stefacep/PLUMA-Hotend-Shroud/Photos/1.JPG

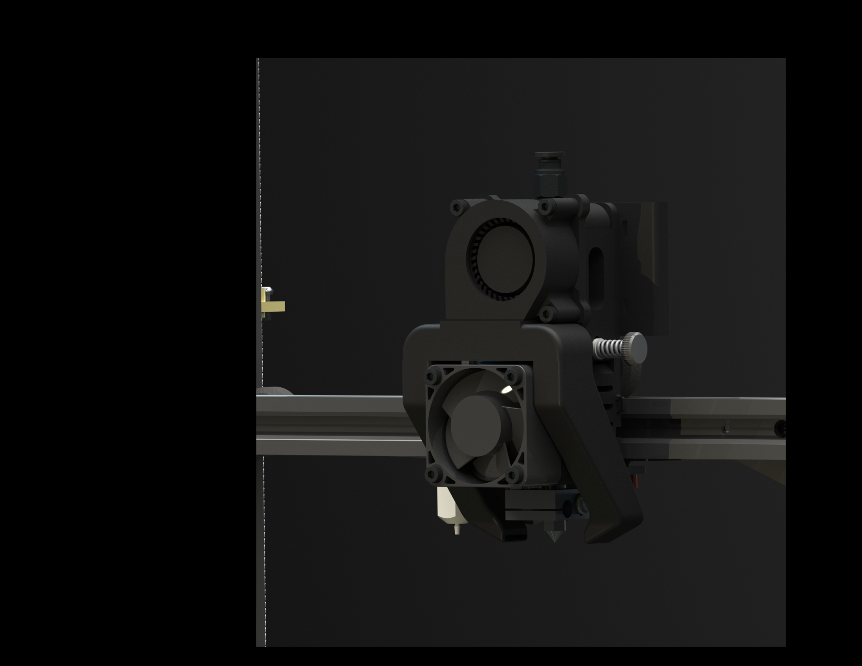
Photos/1.JPG
