stefacep/PLUMA-Hotend-Shroud/Photos/2.jpg

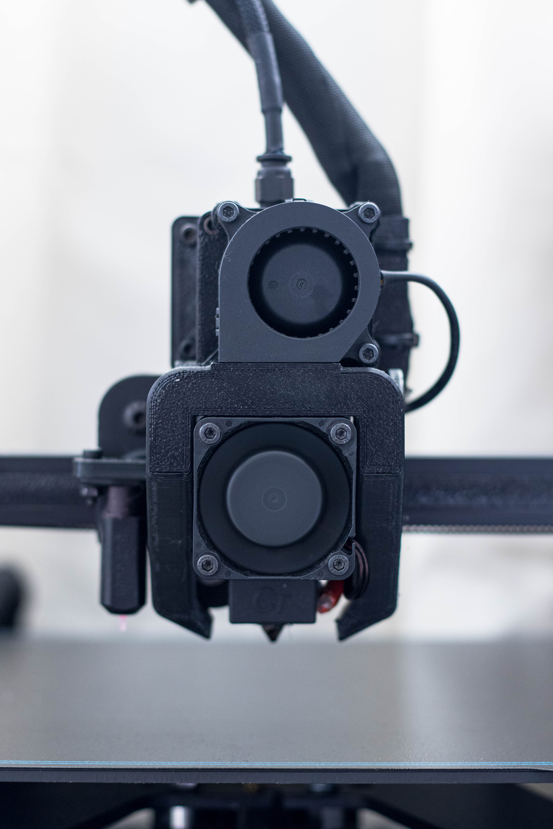
Photos/2.jpg
