stefacep/PLUMA-Hotend-Shroud/Photos/3.jpg

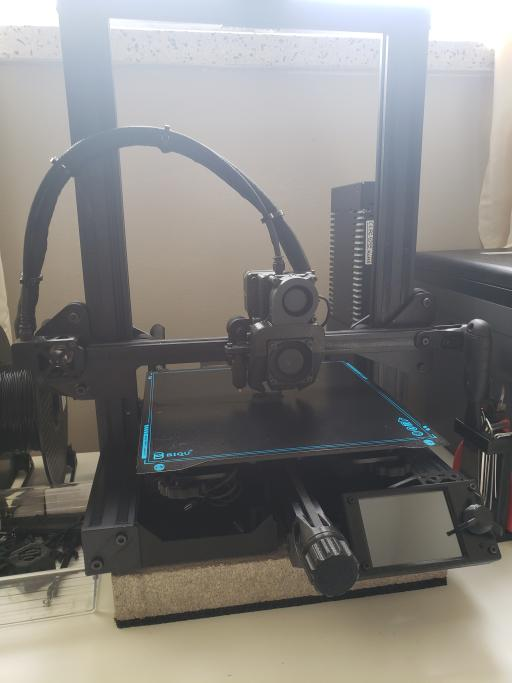
Photos/3.jpg
