stefacep/PLUMA-Hotend-Shroud/Photos/4.jpg

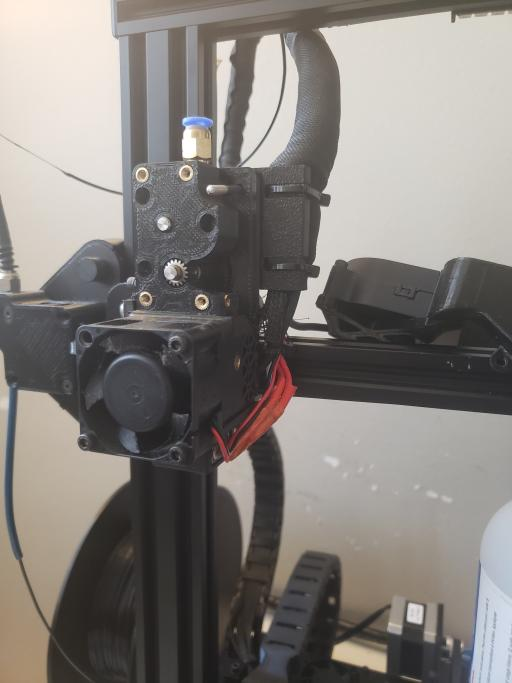
Photos/4.jpg
