stefacep/PLUMA-Hotend-Shroud/Photos/5.jpg

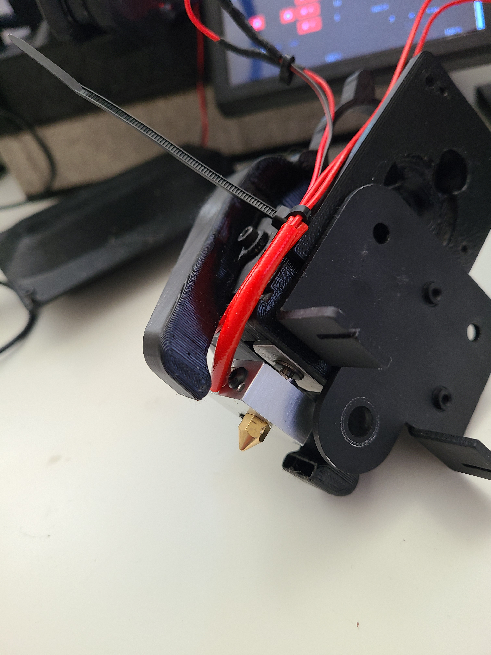
Photos/5.jpg
