stefacep/PLUMA-Hotend-Shroud/Photos/IMG_1597.jpg

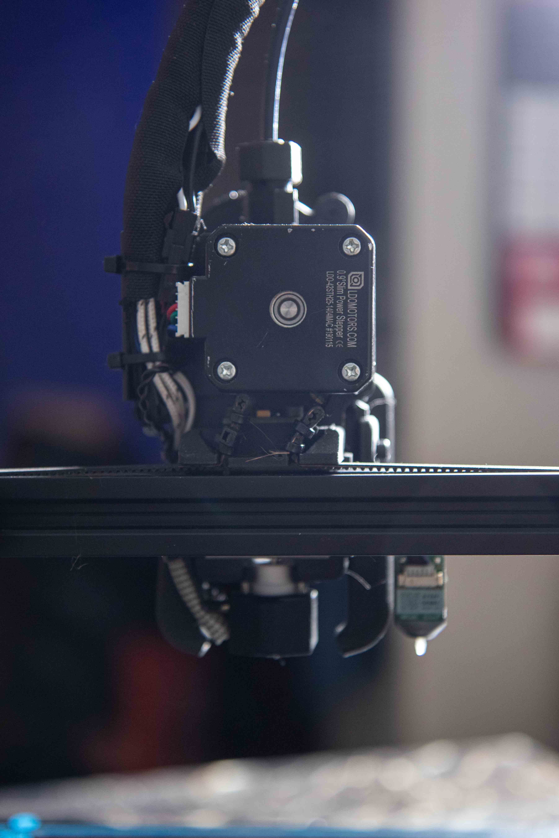
Photos/IMG_1597.jpg
