stefacep/PLUMA-Hotend-Shroud/Photos/IMG_1599.jpg

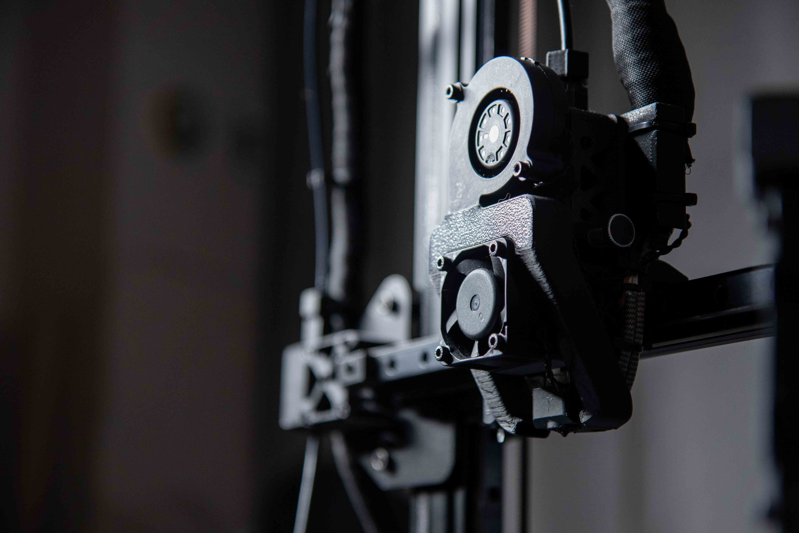
Photos/IMG_1599.jpg
