stefacep/PLUMA-Hotend-Shroud/Photos/IMG_1613.jpg

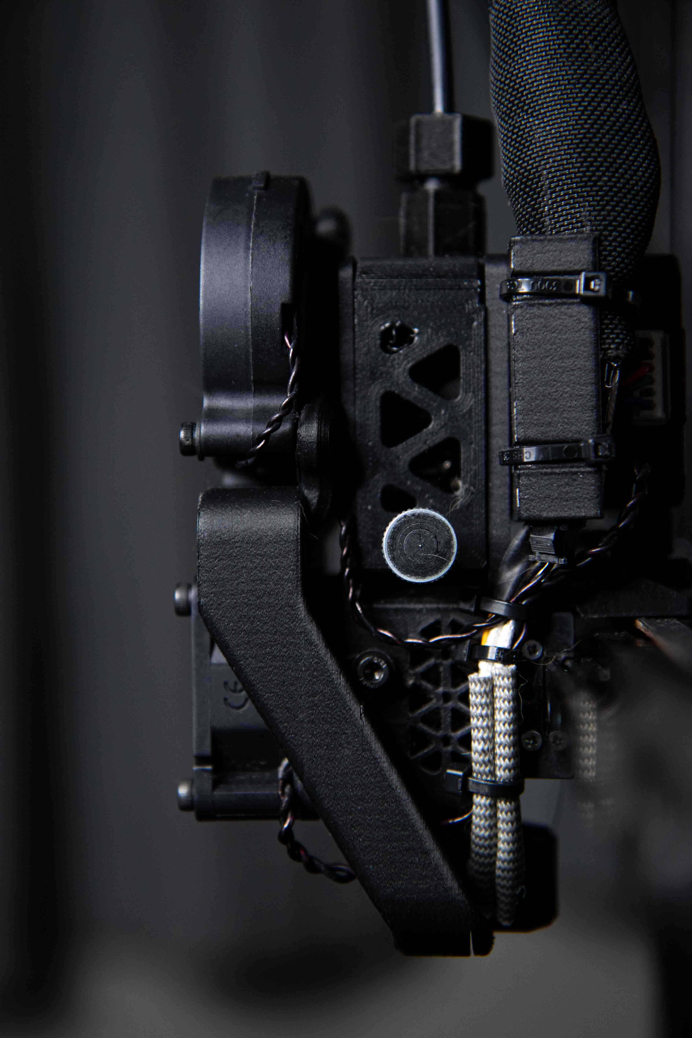
Photos/IMG_1613.jpg
