stefacep/PLUMA-Hotend-Shroud/Photos/IMG_1614.jpg

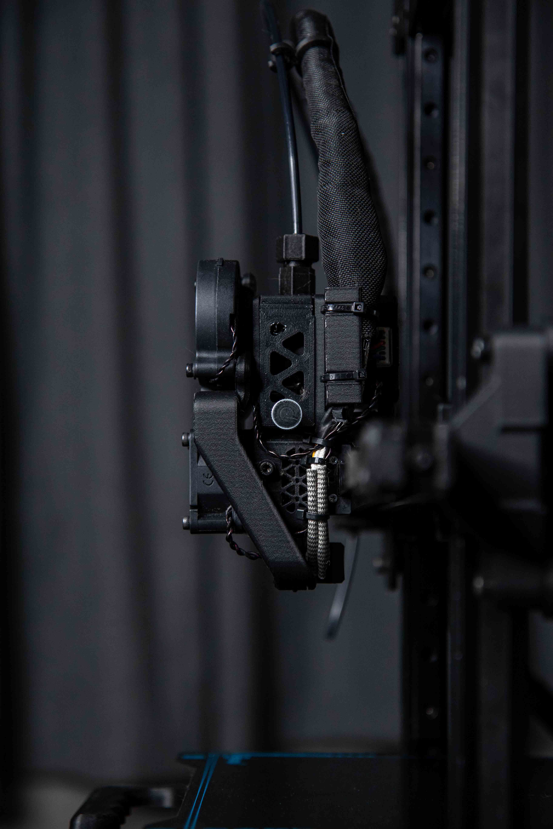
Photos/IMG_1614.jpg
